leedavis-irl/task-tracker/3d/desk-e-ink-weather-display-model_files/v1/frame.stl

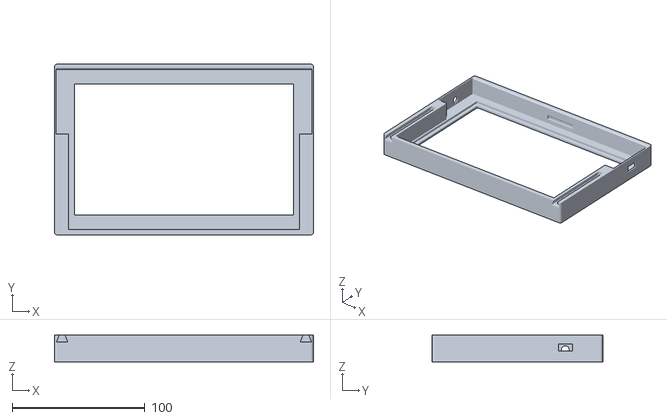
[picture p17: CAD file, 2026-03-18, an earlier design]
3d/desk-e-ink-weather-display-model_files/v1/frame.stl
195.0 x 128.5 x 20.0
